Cirromulus/mimu/sw/include/config.hpp

#pragma once
#include <pins.hpp>
#include <inttypes.h>

using Distance_mm = uint16_t;

static constexpr uint32_t CPU_FREQ = F_CPU;
static constexpr Distance_mm MAX_RANGE_MM = 700;
static constexpr Distance_mm DEBOUNCE_RANGE_MM = 10;
static constexpr Distance_mm DEADZONE_LOW_MM = 40;         // How long is the average microphone? :D
static constexpr uint16_t MAX_ANALOG_READ = 0x3FF;	//10 bit
// Default: 33ms. Min 20ms, Max ~200ms
static constexpr uint32_t MEASUREMENT_TIMING_BUDGET_US = 60000;
static constexpr uint8_t  MEASUREMENT_EXTRA_DELAY_MS = 10;   // to save power
static constexpr uint16_t TOT_MEAS_CYCLE_MS =
        MEASUREMENT_TIMING_BUDGET_US / 1000 + MEASUREMENT_EXTRA_DELAY_MS;
static constexpr uint16_t SENSOR_COMM_TIMEOUT_MS =
        max(100, 1.5*TOT_MEAS_CYCLE_MS);
static constexpr uint8_t  FILTER_EQUAL_DECISIONS_NEEDED = 1;
static constexpr uint8_t  CONSECUTIVE_TIMEOUTS_WARNING = 2;

template <auto val>
constexpr void static_print() {
    #if !defined(__GNUC__) || defined(__clang__)
        int static_print_is_implemented_only_for_gcc = 0;
    #else
        int unused = 0;
    #endif
};
