Cirromulus/mimu/sw/src/userInterface.cpp

#include "userInterface.hpp"

void ui::init() {
    pinMode(LEDR, OUTPUT);
    pinMode(LEDG, OUTPUT);
    digitalWrite(LEDR, 0);
    digitalWrite(LEDG, 0);
}

void ui::waitingForSerial(){
    digitalWrite(LEDR, 1);
    delay(250);
    digitalWrite(LEDR, 0);
    delay(25);
    digitalWrite(LEDG, 1);
    delay(250);
    digitalWrite(LEDG, 0);
    delay(25);
}

void ui::waitingForSensor(){
    digitalWrite(LEDR, 1);
    delay(50);
    digitalWrite(LEDR, 0);
    delay(50);
}

void ui::errorSettingSensorSetting(){
    digitalWrite(LEDR, 1);
    delay(350);
    digitalWrite(LEDR, 0);
    delay(100);
}

// Intentionally delays a bit to let capacitors charge up
void ui::switchOn() {
    for(uint8_t i = 0; i < 2; i++)
    {
        digitalWrite(LEDG, 1);
        delay(50);
        digitalWrite(LEDG, 0);
        delay(50);
    }

    delay(1500);

    digitalWrite(LEDG, 1);
    delay(100);
    digitalWrite(LEDG, 0);
}

void ui::ready() {
    digitalWrite(LEDG, 1);
    delay(200);
    digitalWrite(LEDG, 0);
    delay(50);
}

void ui::sensorCommunicationError() {
    if constexpr (has_serial)
        if (Serial) Serial.println("ToF Timeout.");

    for(uint8_t i = 0; i < 2; i++)
    {
        digitalWrite(LEDR, 1);
        delay(200);
        digitalWrite(LEDR, 0);
        delay(100);
    }
    delay(300);
}

void ui::digipotCommunicationError(const AD5258::TwiReturnStatus return_status) {
    if constexpr (has_serial)
        if (Serial) Serial.println("Digipot comm error.");
    for(uint8_t i = 0; i < 3; i++)
    {
        digitalWrite(LEDR, 1);
        delay(200);
        digitalWrite(LEDR, 0);
        delay(100);
    }
    delay(200);
    for(uint8_t i = return_status; i > 0; i--) {
        digitalWrite(LEDR, 1);
        delay(100);
        digitalWrite(LEDR, 0);
        delay(100);
    }
    delay(400);
}

void ui::settingDistance(const bool is_setting) {
    if (is_setting) {
        digitalWrite(LEDG, (millis() % 512) > 256);
    }
    else {
        // Success we saved it (probably)
        for(uint8_t i = 2; i > 0; i--) {
            digitalWrite(LEDG, 1);
            delay(100);
            digitalWrite(LEDG, 0);
            delay(100);
        }
    }
}

void ui::muted(const bool muted) {
    // might be green on "soft mute" someday
    digitalWrite(LEDR, muted);
}
